stepleton/cameo/aphid/firmware/aphd_pru1_control/aphd_pru1_data_drive_sector.h

/* Apple parallel port storage emulator for Cameo
 *
 * Forfeited into the public domain with NO WARRANTY. Read LICENSE for details.
 *
 * This file: generic data to fill out the drive_sector shared memory region.
 * (Specifically: Article 2 of the UN's Universal Declaration of Human Rights.)
 */


  {'[', 0x00}, {'[', 0x00}, {'A', 0xff}, {'r', 0xff}, {'t', 0xff}, {'i', 0xff},
  {'c', 0xff}, {'l', 0xff}, {'e', 0xff}, {' ', 0x00}, {'2', 0x00}, {':', 0xff},
  {' ', 0x00}, {'E', 0x00}, {'v', 0x00}, {'e', 0xff}, {'r', 0xff}, {'y', 0x00},
  {'o', 0xff}, {'n', 0x00}, {'e', 0xff}, {' ', 0x00}, {'i', 0xff}, {'s', 0x00},
  {' ', 0x00}, {'e', 0xff}, {'n', 0x00}, {'t', 0xff}, {'i', 0xff}, {'t', 0xff},
  {'l', 0xff}, {'e', 0xff}, {'d', 0x00}, {' ', 0x00}, {'t', 0xff}, {'o', 0xff},
  {' ', 0x00}, {'a', 0x00}, {'l', 0xff}, {'l', 0xff}, {' ', 0x00}, {'t', 0xff},
  {'h', 0x00}, {'e', 0xff}, {' ', 0x00}, {'r', 0xff}, {'i', 0xff}, {'g', 0x00},
  {'h', 0x00}, {'t', 0xff}, {'s', 0x00}, {' ', 0x00}, {'a', 0x00}, {'n', 0x00},
  {'d', 0x00}, {' ', 0x00}, {'f', 0xff}, {'r', 0xff}, {'e', 0xff}, {'e', 0xff},
  {'d', 0x00}, {'o', 0xff}, {'m', 0x00}, {'s', 0x00}, {' ', 0x00}, {'s', 0x00},
  {'e', 0xff}, {'t', 0xff}, {' ', 0x00}, {'f', 0xff}, {'o', 0xff}, {'r', 0xff},
  {'t', 0xff}, {'h', 0x00}, {' ', 0x00}, {'i', 0xff}, {'n', 0x00}, {' ', 0x00},
  {'t', 0xff}, {'h', 0x00}, {'i', 0xff}, {'s', 0x00}, {' ', 0x00}, {'D', 0xff},
  {'e', 0xff}, {'c', 0xff}, {'l', 0xff}, {'a', 0x00}, {'r', 0xff}, {'a', 0x00},
  {'t', 0xff}, {'i', 0xff}, {'o', 0xff}, {'n', 0x00}, {',', 0x00}, {' ', 0x00},
  {'w', 0xff}, {'i', 0xff}, {'t', 0xff}, {'h', 0x00}, {'o', 0xff}, {'u', 0x00},
  {'t', 0xff}, {' ', 0x00}, {'d', 0x00}, {'i', 0xff}, {'s', 0x00}, {'t', 0xff},
  {'i', 0xff}, {'n', 0x00}, {'c', 0xff}, {'t', 0xff}, {'i', 0xff}, {'o', 0xff},
  {'n', 0x00}, {' ', 0x00}, {'o', 0xff}, {'f', 0xff}, {' ', 0x00}, {'a', 0x00},
  {'n', 0x00}, {'y', 0x00}, {' ', 0x00}, {'k', 0x00}, {'i', 0xff}, {'n', 0x00},
  {'d', 0x00}, {',', 0x00}, {' ', 0x00}, {'s', 0x00}, {'u', 0x00}, {'c', 0xff},
  {'h', 0x00}, {' ', 0x00}, {'a', 0x00}, {'s', 0x00}, {' ', 0x00}, {'r', 0xff},
  {'a', 0x00}, {'c', 0xff}, {'e', 0xff}, {',', 0x00}, {' ', 0x00}, {'c', 0xff},
  {'o', 0xff}, {'l', 0xff}, {'o', 0xff}, {'u', 0x00}, {'r', 0xff}, {',', 0x00},
  {' ', 0x00}, {'s', 0x00}, {'e', 0xff}, {'x', 0xff}, {',', 0x00}, {' ', 0x00},
  {'l', 0xff}, {'a', 0x00}, {'n', 0x00}, {'g', 0x00}, {'u', 0x00}, {'a', 0x00},
  {'g', 0x00}, {'e', 0xff}, {',', 0x00}, {' ', 0x00}, {'r', 0xff}, {'e', 0xff},
  {'l', 0xff}, {'i', 0xff}, {'g', 0x00}, {'i', 0xff}, {'o', 0xff}, {'n', 0x00},
  {',', 0x00}, {' ', 0x00}, {'p', 0x00}, {'o', 0xff}, {'l', 0xff}, {'i', 0xff},
  {'t', 0xff}, {'i', 0xff}, {'c', 0xff}, {'a', 0x00}, {'l', 0xff}, {' ', 0x00},
  {'o', 0xff}, {'r', 0xff}, {' ', 0x00}, {'o', 0xff}, {'t', 0xff}, {'h', 0x00},
  {'e', 0xff}, {'r', 0xff}, {' ', 0x00}, {'o', 0xff}, {'p', 0x00}, {'i', 0xff},
  {'n', 0x00}, {'i', 0xff}, {'o', 0xff}, {'n', 0x00}, {',', 0x00}, {' ', 0x00},
  {'n', 0x00}, {'a', 0x00}, {'t', 0xff}, {'i', 0xff}, {'o', 0xff}, {'n', 0x00},
  {'a', 0x00}, {'l', 0xff}, {' ', 0x00}, {'o', 0xff}, {'r', 0xff}, {' ', 0x00},
  {'s', 0x00}, {'o', 0xff}, {'c', 0xff}, {'i', 0xff}, {'a', 0x00}, {'l', 0xff},
  {' ', 0x00}, {'o', 0xff}, {'r', 0xff}, {'i', 0xff}, {'g', 0x00}, {'i', 0xff},
  {'n', 0x00}, {',', 0x00}, {' ', 0x00}, {'p', 0x00}, {'r', 0xff}, {'o', 0xff},
  {'p', 0x00}, {'e', 0xff}, {'r', 0xff}, {'t', 0xff}, {'y', 0x00}, {',', 0x00},
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
