stepleton/cameo/aphid/firmware/aphd_pru1_control/aphd_pru1_data_bytes_with_parity.h

/* Apple parallel port storage emulator for Cameo
 *
 * Forfeited into the public domain with NO WARRANTY. Read LICENSE for details.
 *
 * This file: parity table to fill the bytes_with_parity shared memory region.
 */


        {0x00, 0xff}, {0x01, 0x00}, {0x02, 0x00}, {0x03, 0xff},
        {0x04, 0x00}, {0x05, 0xff}, {0x06, 0xff}, {0x07, 0x00},
        {0x08, 0x00}, {0x09, 0xff}, {0x0a, 0xff}, {0x0b, 0x00},
        {0x0c, 0xff}, {0x0d, 0x00}, {0x0e, 0x00}, {0x0f, 0xff},

        {0x10, 0x00}, {0x11, 0xff}, {0x12, 0xff}, {0x13, 0x00},
        {0x14, 0xff}, {0x15, 0x00}, {0x16, 0x00}, {0x17, 0xff},
        {0x18, 0xff}, {0x19, 0x00}, {0x1a, 0x00}, {0x1b, 0xff},
        {0x1c, 0x00}, {0x1d, 0xff}, {0x1e, 0xff}, {0x1f, 0x00},

        {0x20, 0x00}, {0x21, 0xff}, {0x22, 0xff}, {0x23, 0x00},
        {0x24, 0xff}, {0x25, 0x00}, {0x26, 0x00}, {0x27, 0xff},
        {0x28, 0xff}, {0x29, 0x00}, {0x2a, 0x00}, {0x2b, 0xff},
        {0x2c, 0x00}, {0x2d, 0xff}, {0x2e, 0xff}, {0x2f, 0x00},

        {0x30, 0xff}, {0x31, 0x00}, {0x32, 0x00}, {0x33, 0xff},
        {0x34, 0x00}, {0x35, 0xff}, {0x36, 0xff}, {0x37, 0x00},
        {0x38, 0x00}, {0x39, 0xff}, {0x3a, 0xff}, {0x3b, 0x00},
        {0x3c, 0xff}, {0x3d, 0x00}, {0x3e, 0x00}, {0x3f, 0xff},

        {0x40, 0x00}, {0x41, 0xff}, {0x42, 0xff}, {0x43, 0x00},
        {0x44, 0xff}, {0x45, 0x00}, {0x46, 0x00}, {0x47, 0xff},
        {0x48, 0xff}, {0x49, 0x00}, {0x4a, 0x00}, {0x4b, 0xff},
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

        {0xf0, 0xff}, {0xf1, 0x00}, {0xf2, 0x00}, {0xf3, 0xff},
        {0xf4, 0x00}, {0xf5, 0xff}, {0xf6, 0xff}, {0xf7, 0x00},
        {0xf8, 0x00}, {0xf9, 0xff}, {0xfa, 0xff}, {0xfb, 0x00},
        {0xfc, 0xff}, {0xfd, 0x00}, {0xfe, 0x00}, {0xff, 0xff},
